cele9999/RCSnowplow/images/axle-collars.jpg

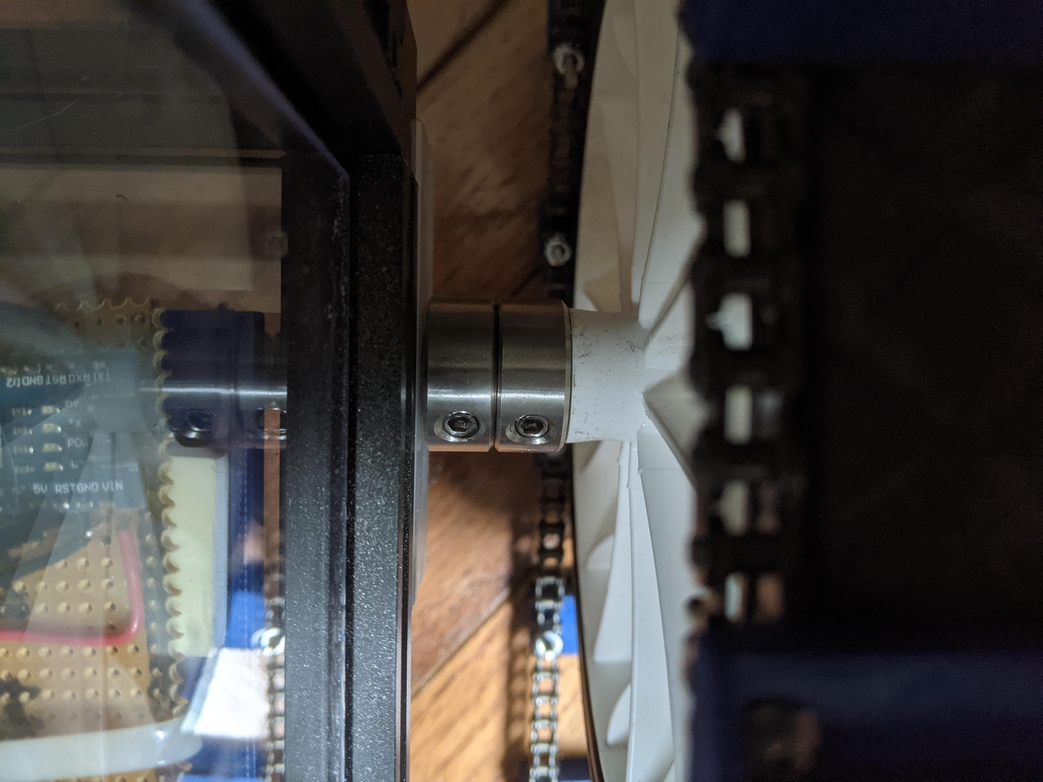
images/axle-collars.jpg
