cele9999/RCSnowplow/images/axle-holders.jpg

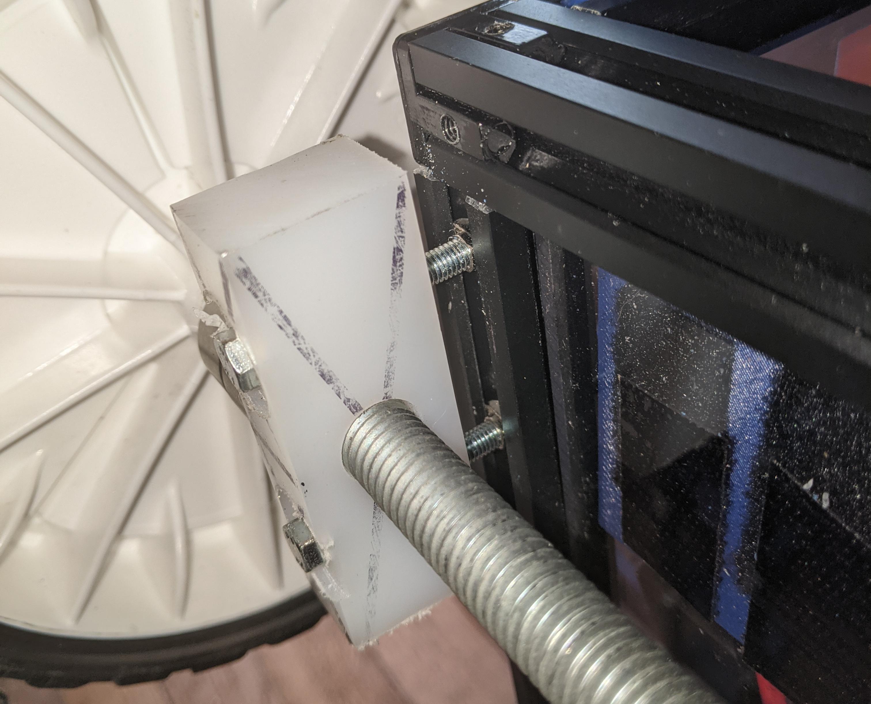
images/axle-holders.jpg
