cele9999/RCSnowplow/images/chainring-alignment1.jpg

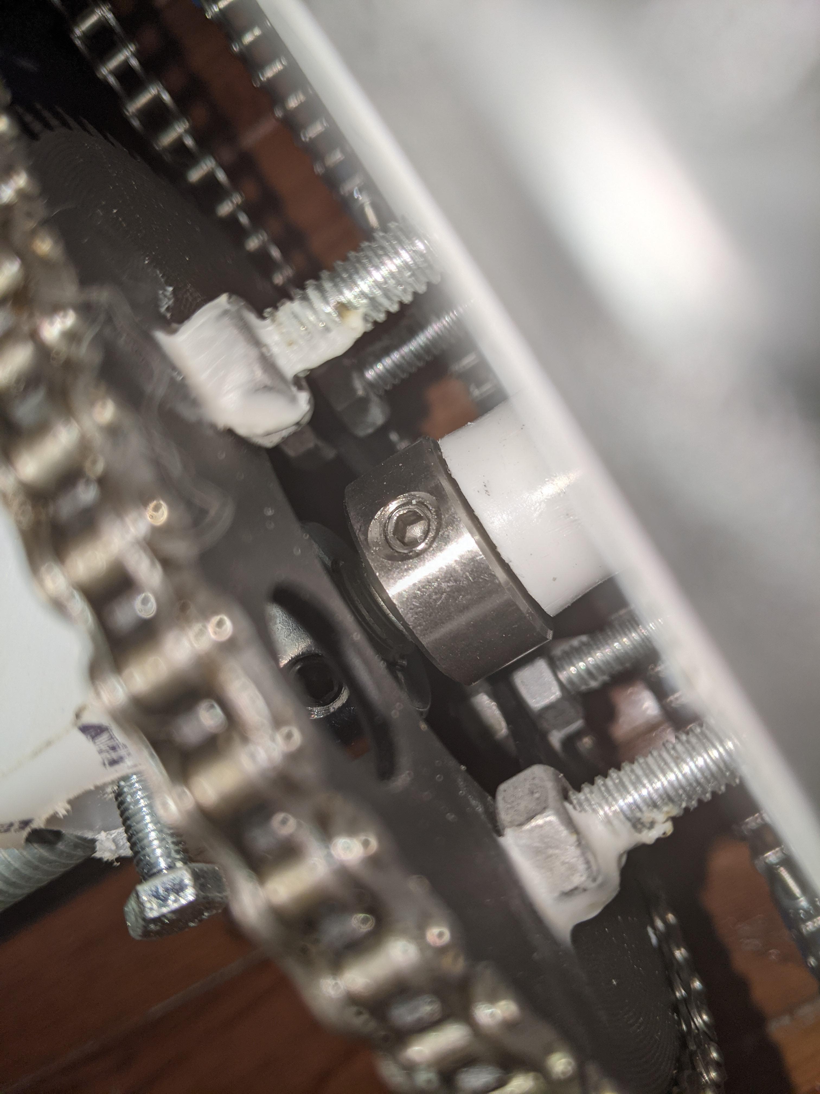
images/chainring-alignment1.jpg
