cele9999/RCSnowplow/images/chainring-alignment2.jpg

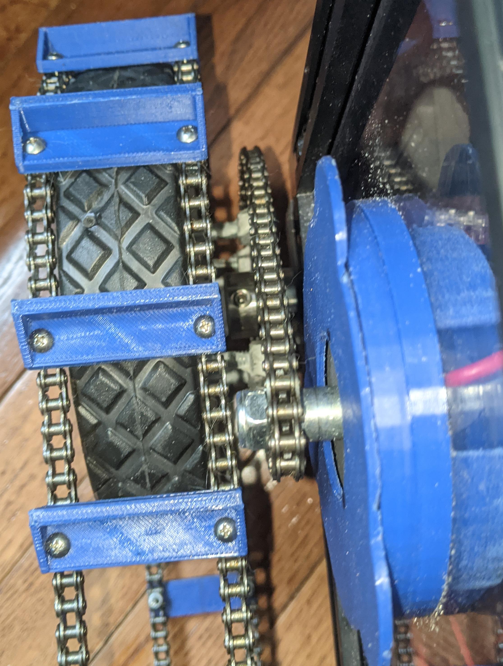
images/chainring-alignment2.jpg
