cele9999/RCSnowplow/images/frame-dimensions.jpg

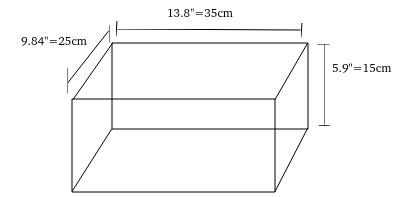
images/frame-dimensions.jpg
