cele9999/RCSnowplow/images/frame.jpg

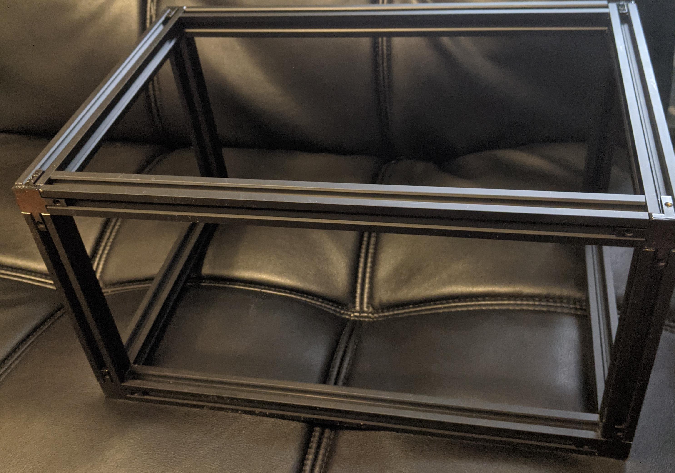
images/frame.jpg
