cele9999/RCSnowplow/images/lid-and-treads.jpg

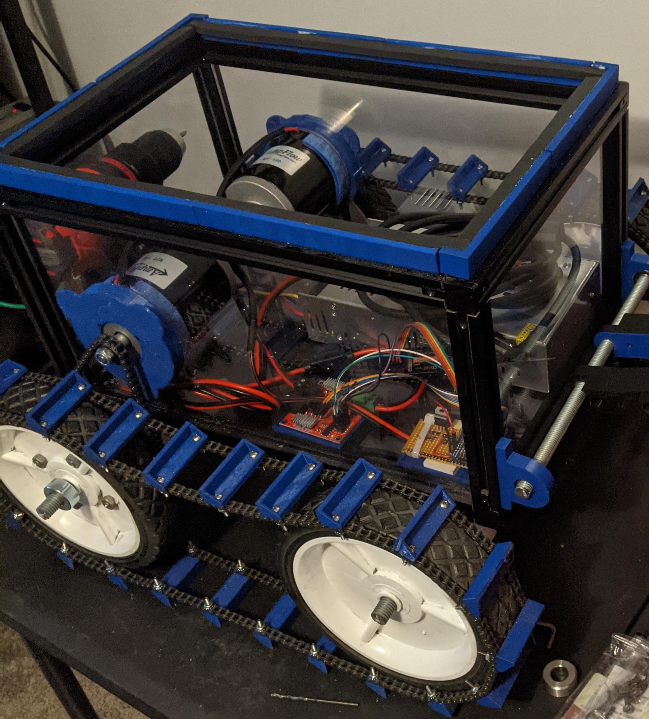
images/lid-and-treads.jpg
