cele9999/RCSnowplow/images/lid-hinge.jpg

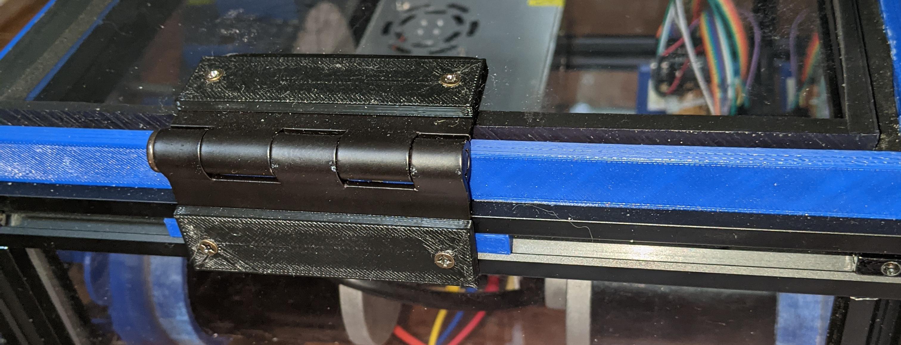
images/lid-hinge.jpg
