cele9999/RCSnowplow/images/linear-actuator1.jpg

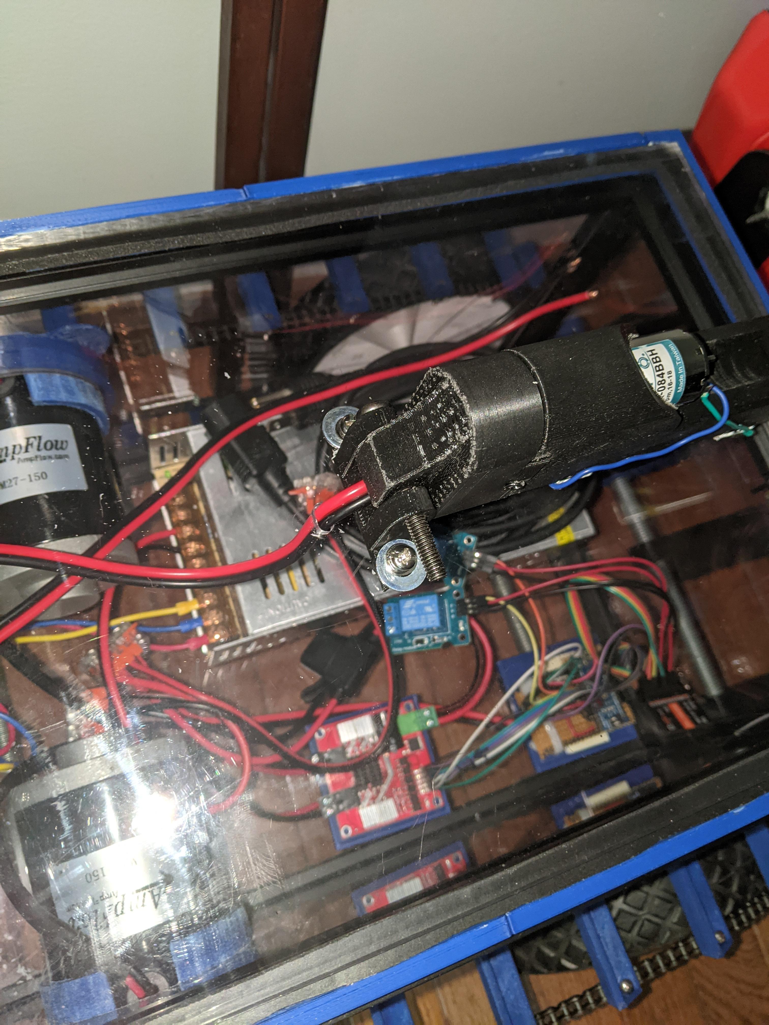
images/linear-actuator1.jpg
