cele9999/RCSnowplow/images/linear-actuator2.jpg

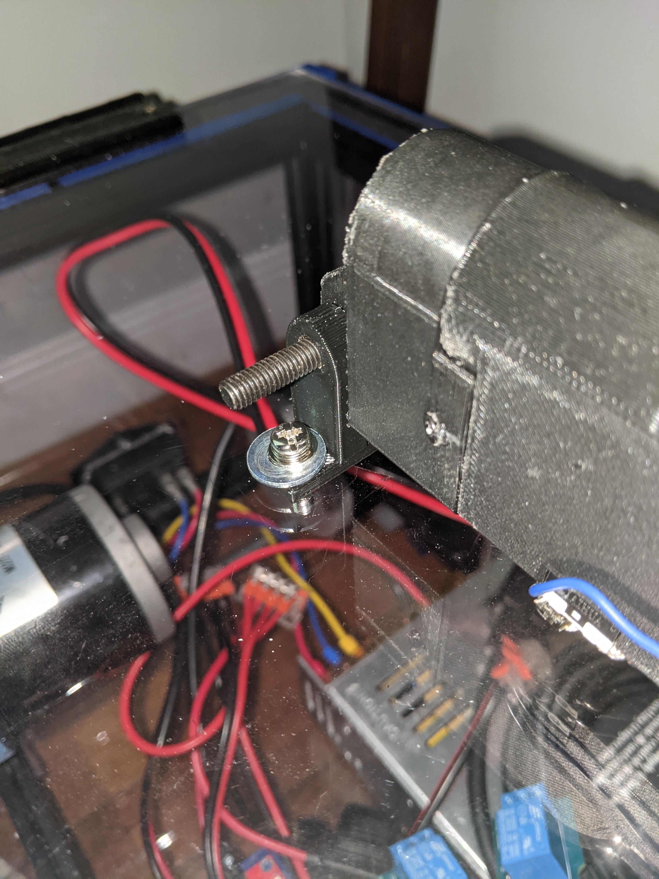
images/linear-actuator2.jpg
