cele9999/RCSnowplow/images/linear-actuator3.jpg

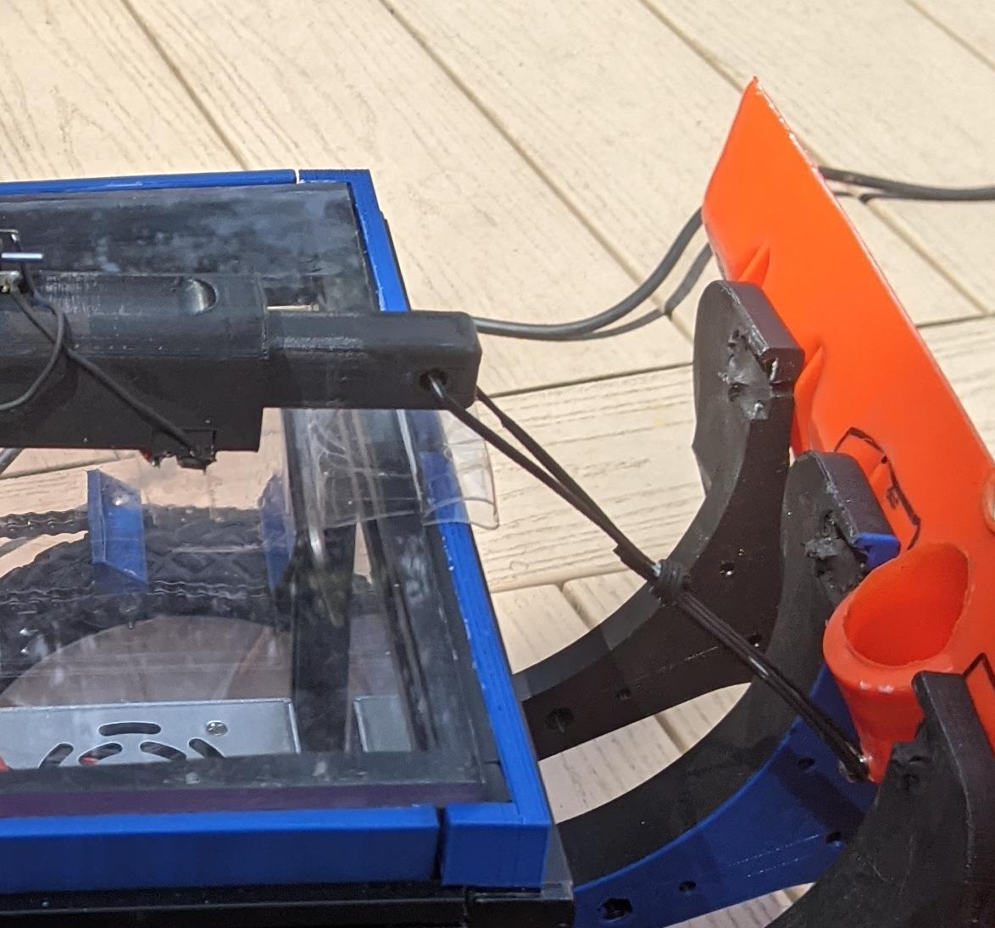
images/linear-actuator3.jpg
