cele9999/RCSnowplow/images/motor-panels.jpg

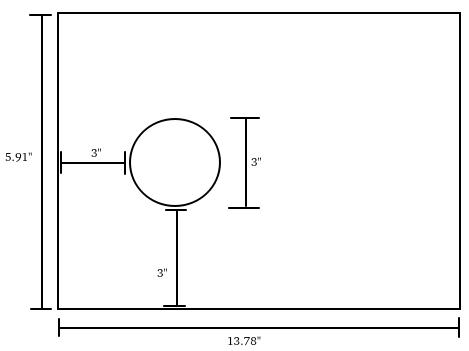
images/motor-panels.jpg
