cele9999/RCSnowplow/images/motor-sleeves.jpg

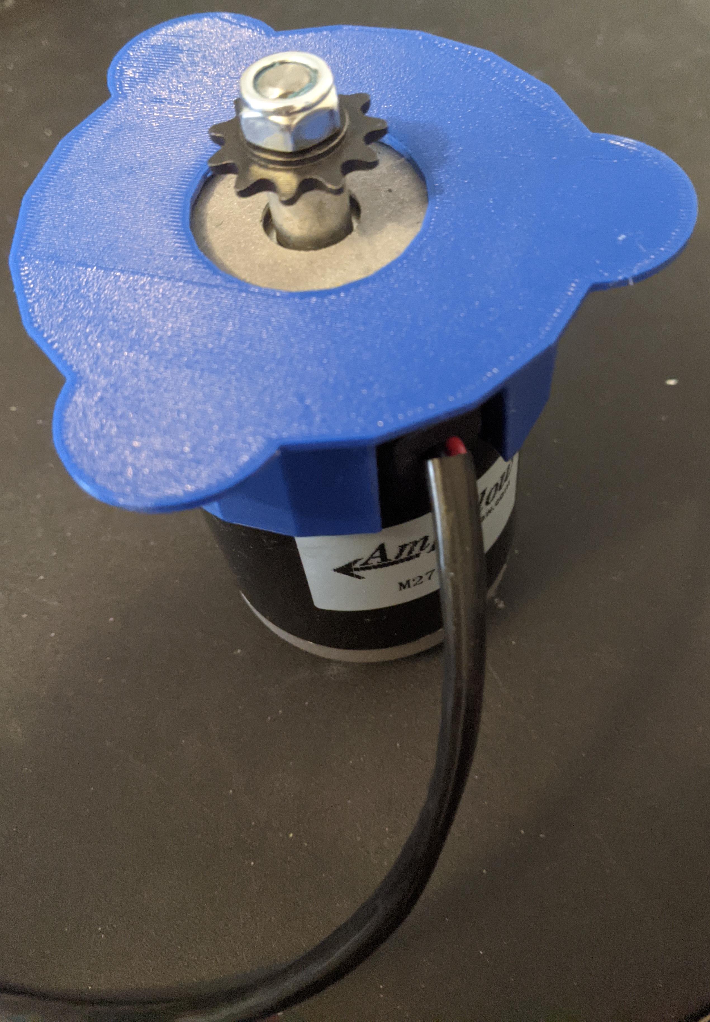
images/motor-sleeves.jpg
