cele9999/RCSnowplow/images/motor-spacers.jpg

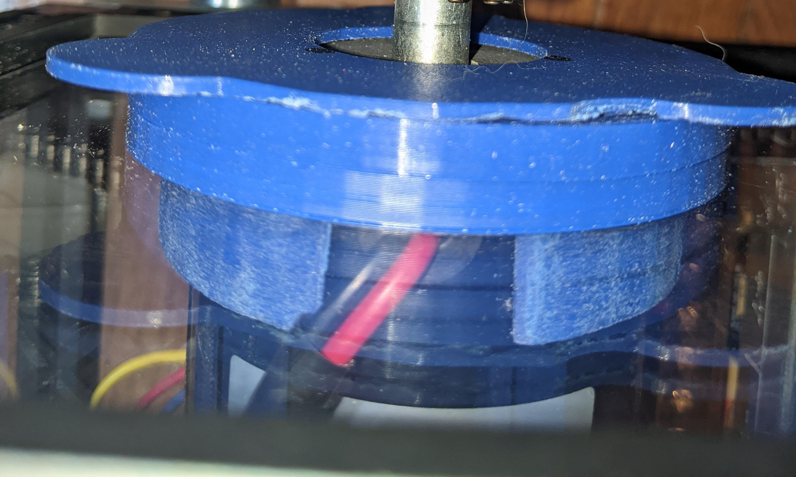
images/motor-spacers.jpg
