cele9999/RCSnowplow/images/outlet-connector1.jpg

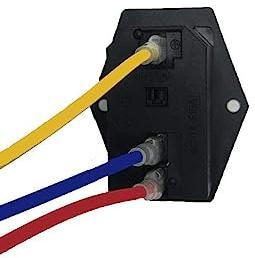
images/outlet-connector1.jpg
