cele9999/RCSnowplow/images/outlet-connector2.jpg

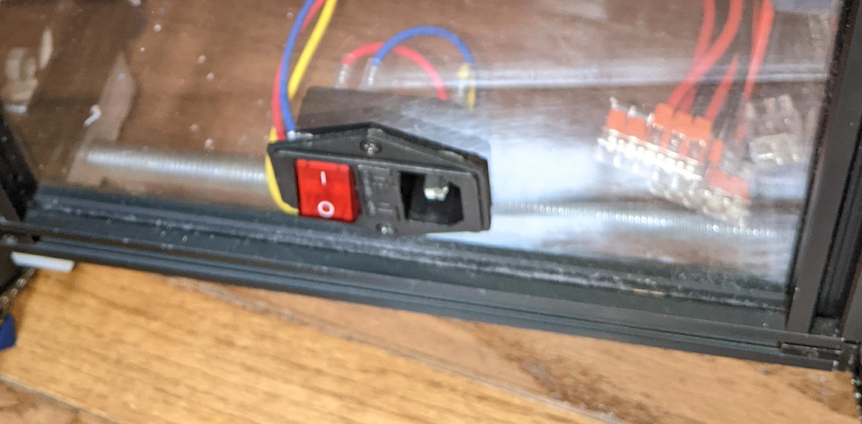
images/outlet-connector2.jpg
