cele9999/RCSnowplow/images/rc-snowmelter2.jpg

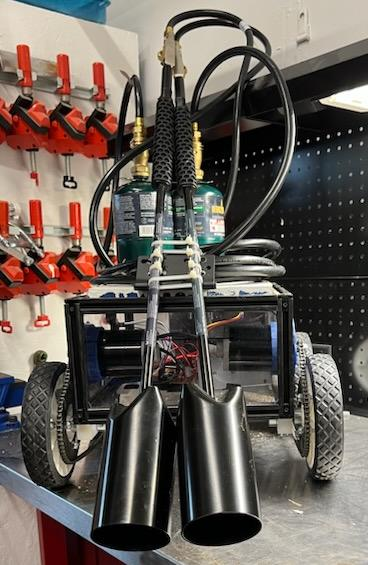
images/rc-snowmelter2.jpg
