cele9999/RCSnowplow/images/rc-snowmelter3.jpg

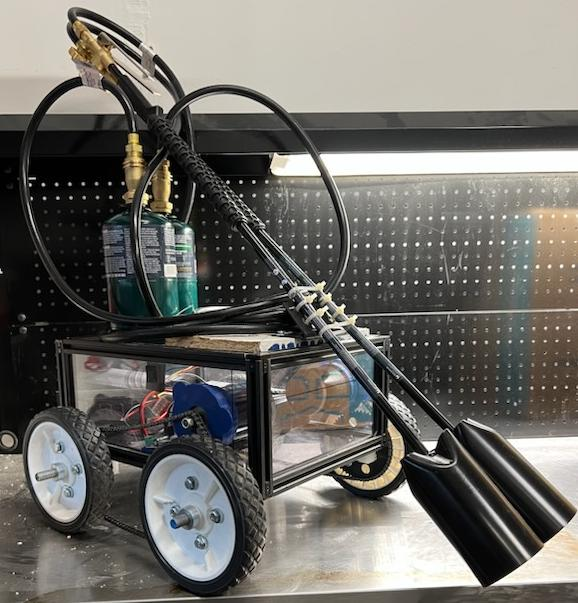
images/rc-snowmelter3.jpg
