cele9999/RCSnowplow/images/snowbyte1.jpg

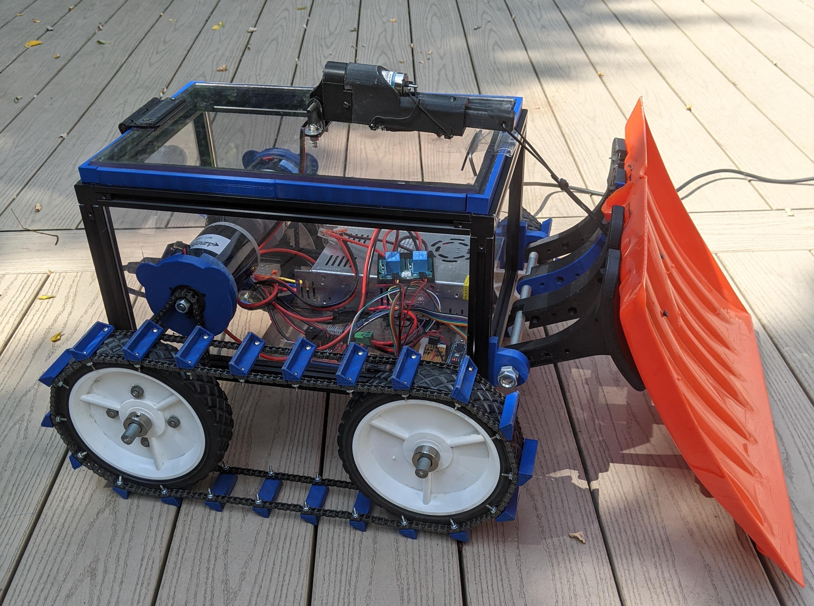
images/snowbyte1.jpg
