cele9999/RCSnowplow/images/snowbyte2.jpg

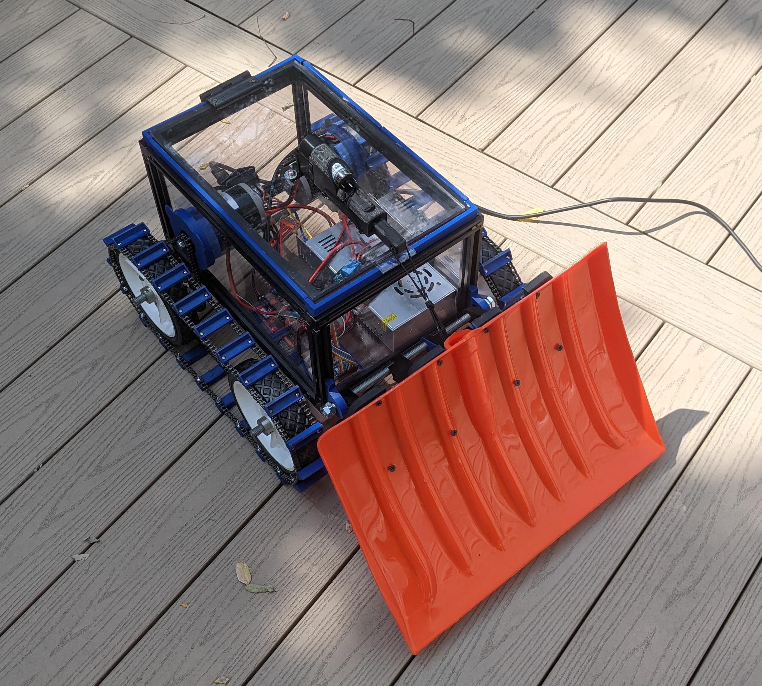
images/snowbyte2.jpg
