cele9999/RCSnowplow/images/snowplow-attachment1.jpg

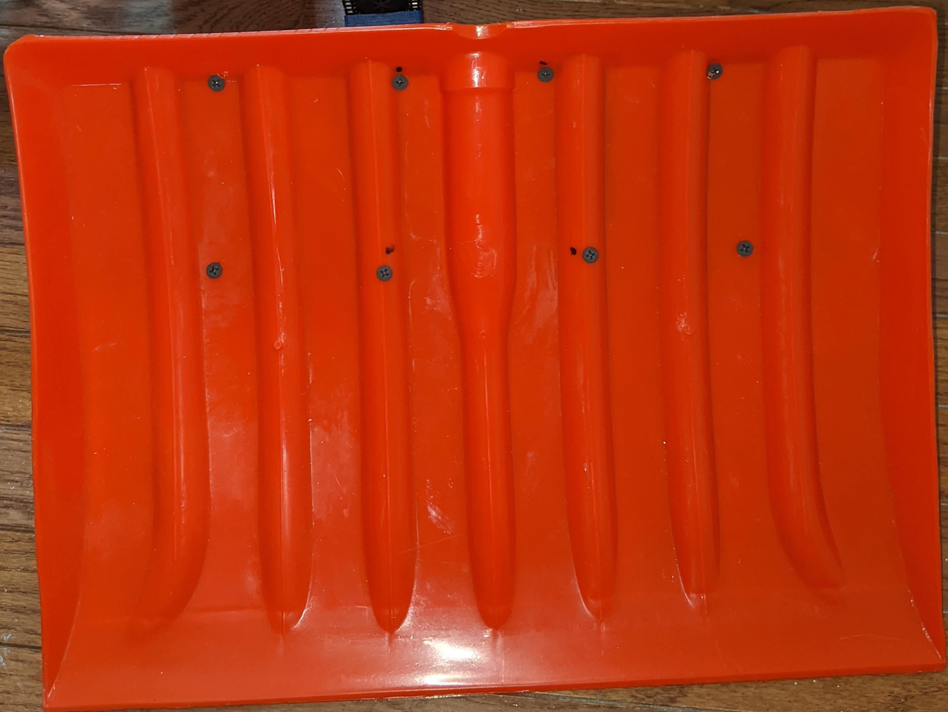
images/snowplow-attachment1.jpg
