cele9999/RCSnowplow/images/top-lid.jpg

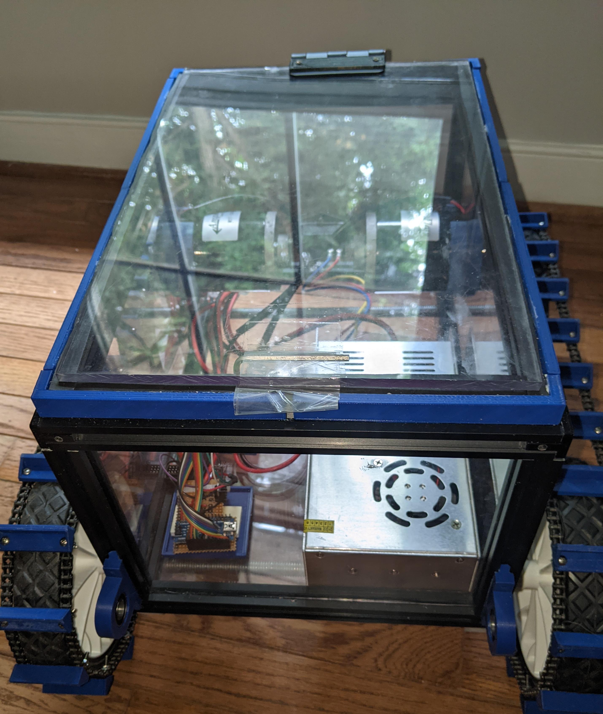
images/top-lid.jpg
