cele9999/RCSnowplow/images/wheel-axles.jpg

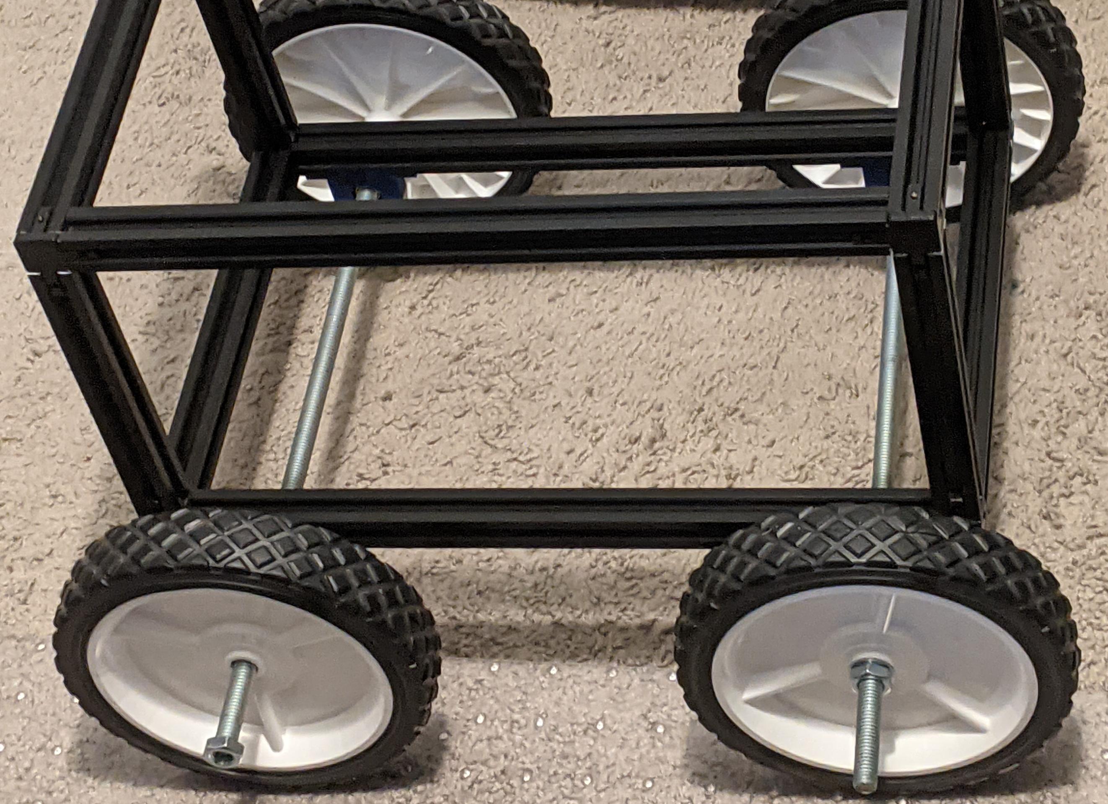
images/wheel-axles.jpg
