cele9999/RCSnowplow/images/wheel-chainring1.jpg

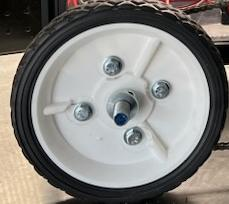
images/wheel-chainring1.jpg
