cele9999/RCSnowplow/images/wheel-chainring2.jpg

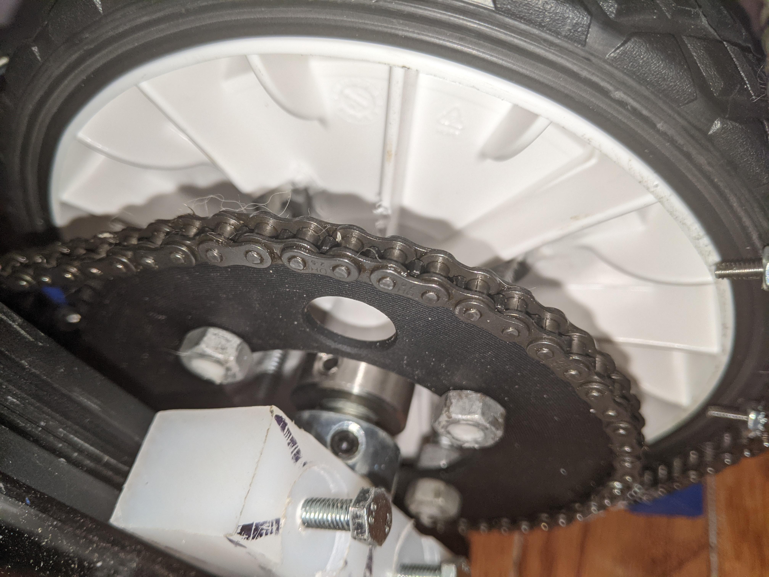
images/wheel-chainring2.jpg
