cele9999/RCSnowplow/images/wheel-sprocket.jpg

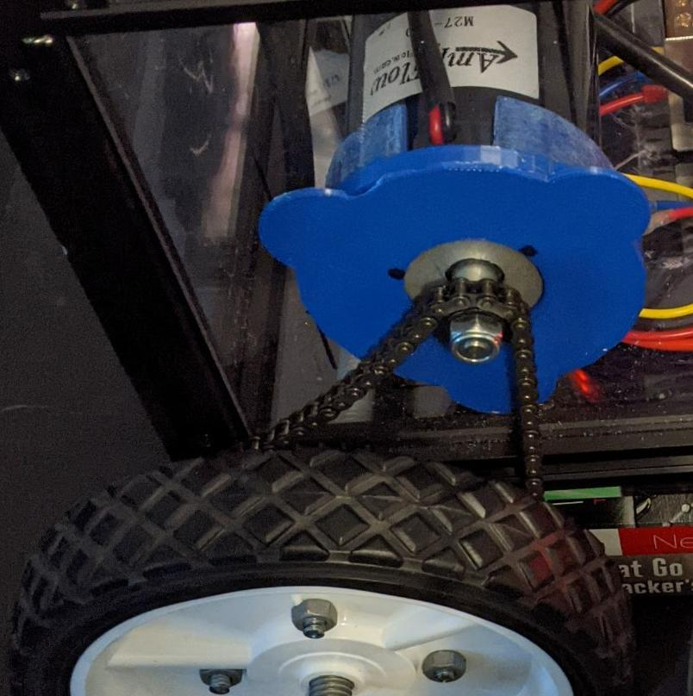
images/wheel-sprocket.jpg
