cele9999/RCSnowplow/3d-print-files/motor-sleeve-spacer.stl

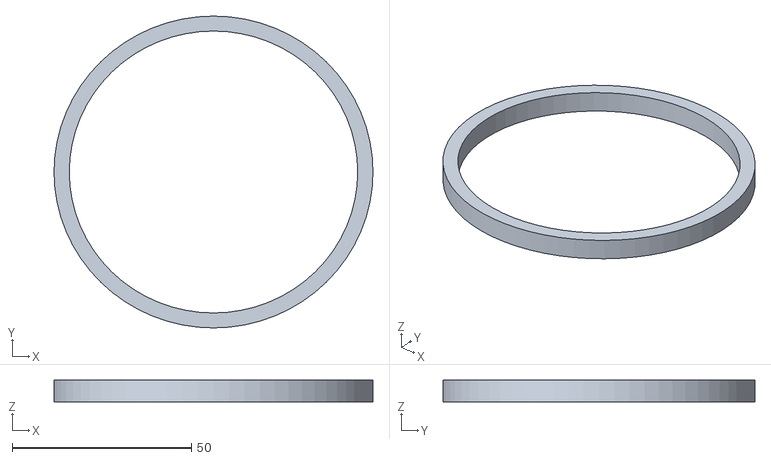
[picture p48: CAD file, 2023-08-09]
3d-print-files/motor-sleeve-spacer.stl
89.0 x 87.0 x 6.00
