cele9999/RCSnowplow/3d-print-files/motor-sleeve-v2.stl

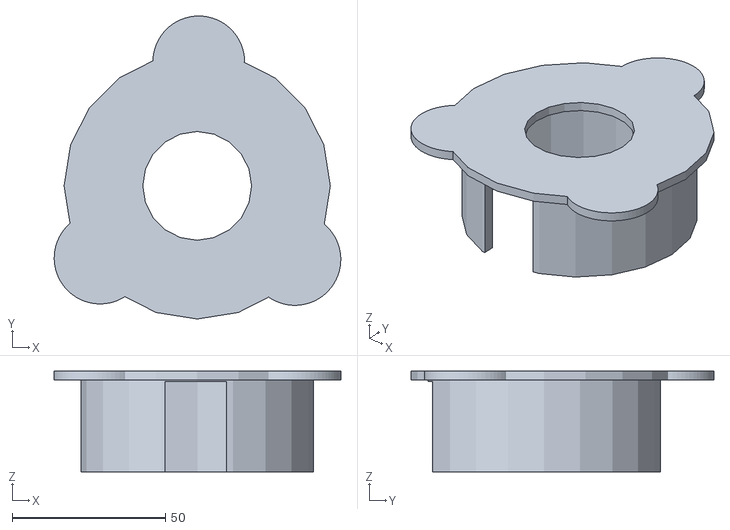
[picture p49: CAD file, 2023-08-09]
3d-print-files/motor-sleeve-v2.stl
93.6 x 99.0 x 33.0
