cele9999/RCSnowplow/3d-print-files/rail-holder.stl

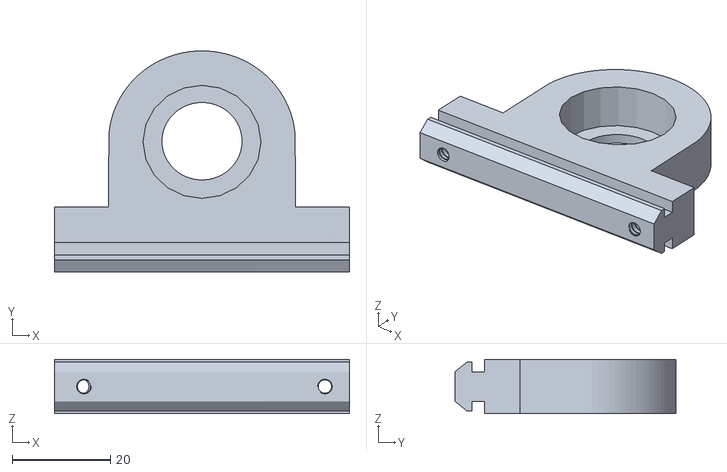
[picture p50: CAD file, 2023-08-09]
3d-print-files/rail-holder.stl
60.0 x 45.0 x 11.0
