cele9999/RCSnowplow/3d-print-files/tank-thread.stl

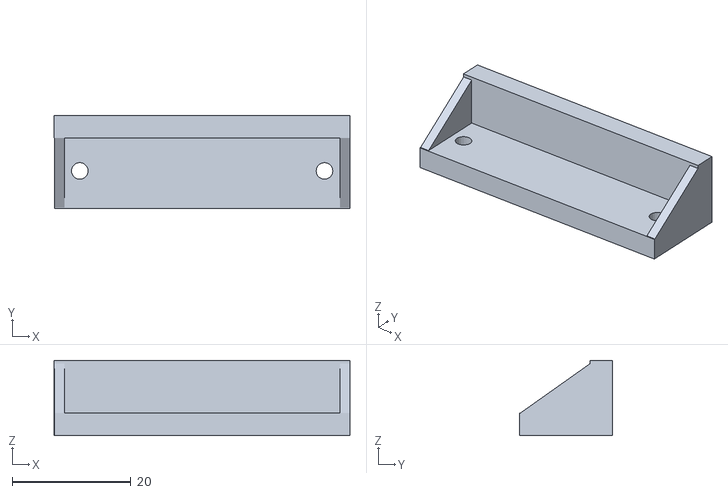
[picture p51: CAD file, 2023-08-09]
3d-print-files/tank-thread.stl
49.9 x 15.7 x 12.7
